frc3223/robot2023/Photos and Videos for RoCK/20230107_090842.jpg

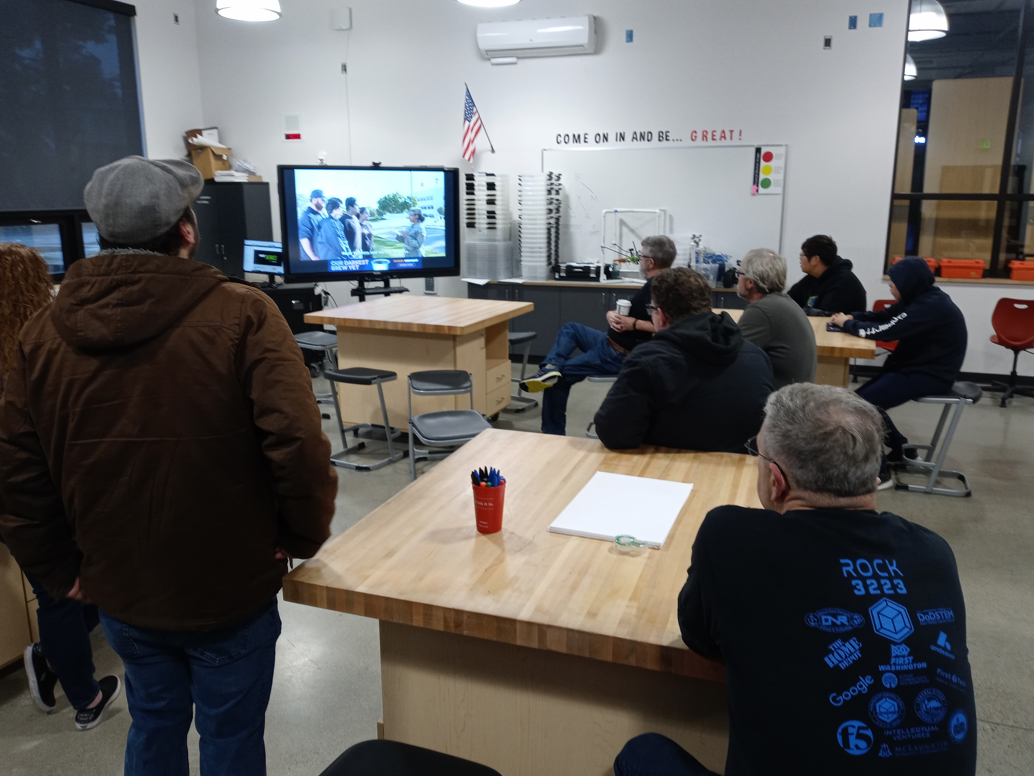
Photos and Videos for RoCK/20230107_090842.jpg
