frc3223/robot2023/Photos and Videos for RoCK/20221025_165955.jpg

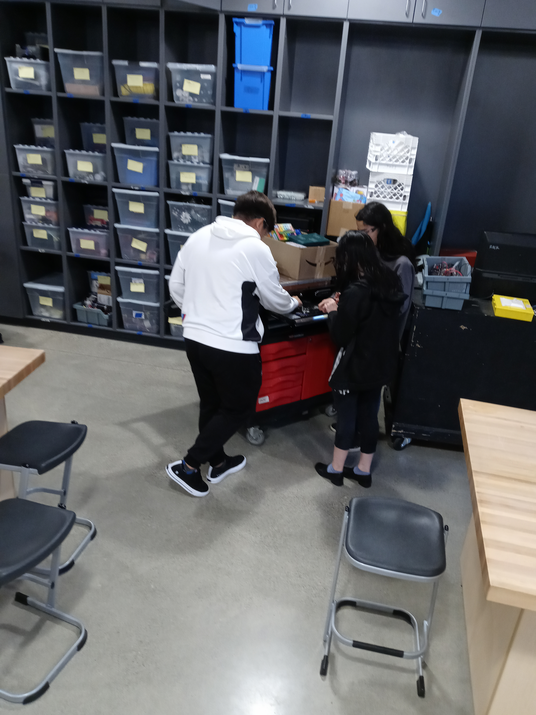
Photos and Videos for RoCK/20221025_165955.jpg
